jcortizronda/huawei_modbusRTU/images/image1.jpg

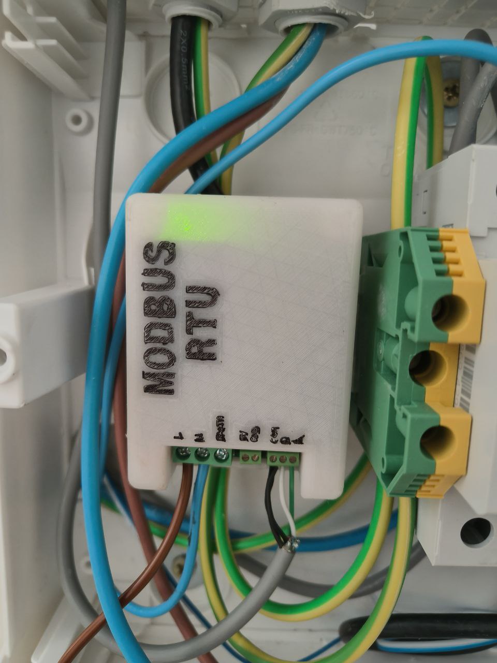
images/image1.jpg
