jcortizronda/huawei_modbusRTU/images/image2.jpg

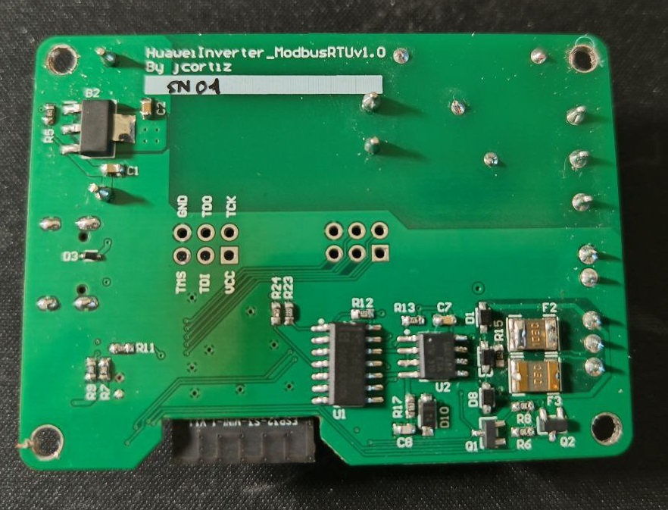
images/image2.jpg
