jcortizronda/huawei_modbusRTU/images/image3.jpg

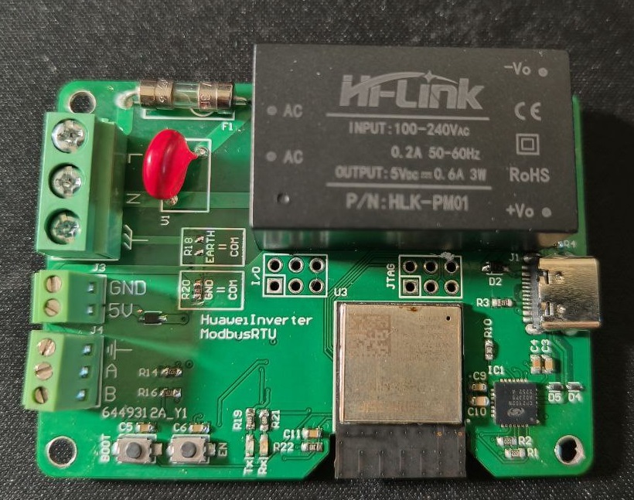
images/image3.jpg
