jcortizronda/huawei_modbusRTU/images/image4.jpg

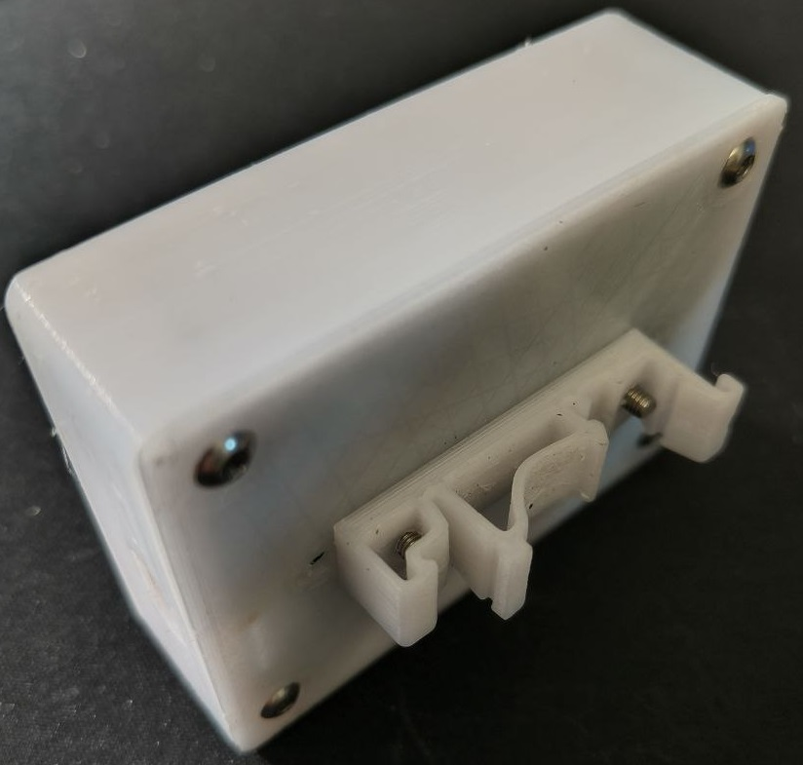
images/image4.jpg
