jcortizronda/huawei_modbusRTU/images/image5.jpg

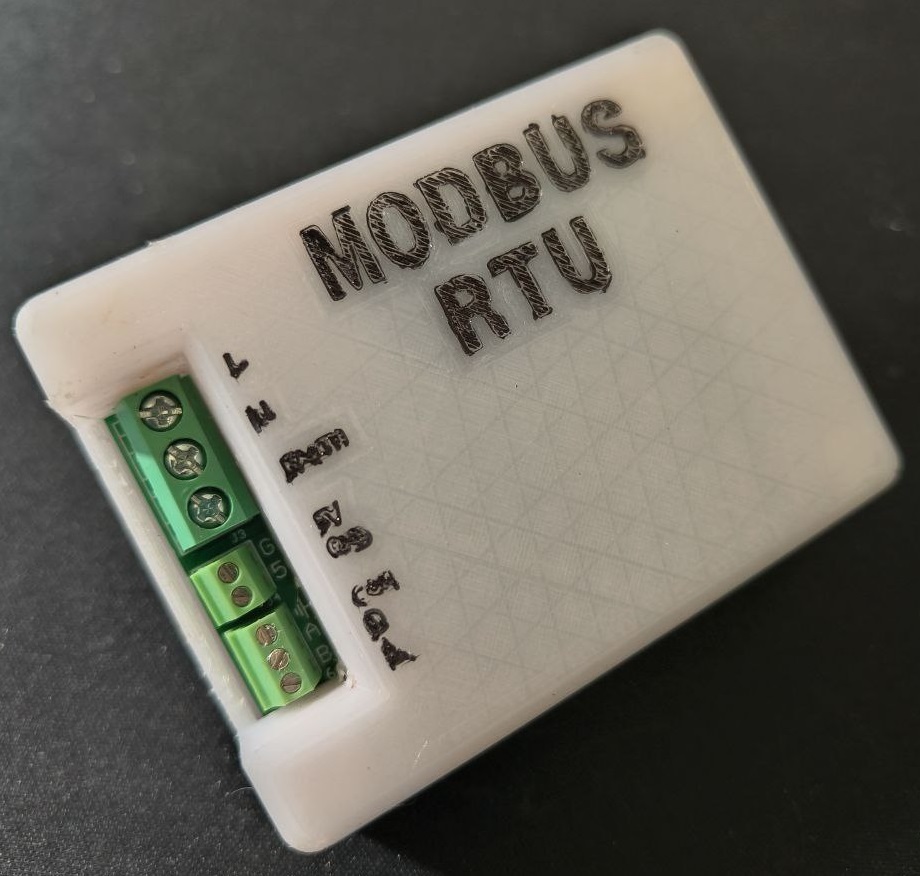
images/image5.jpg
